JolonB/DualSense-Charging-Dock/assets/images/c.jpg

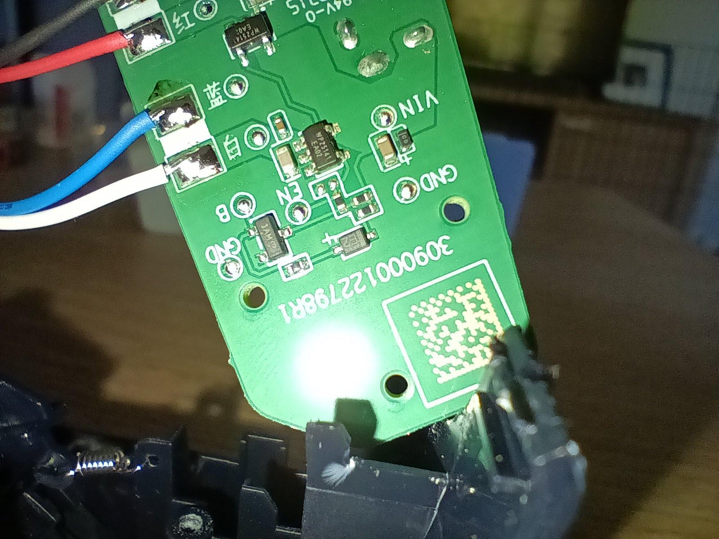
assets/images/c.jpg
