JolonB/DualSense-Charging-Dock/assets/images/g.jpg

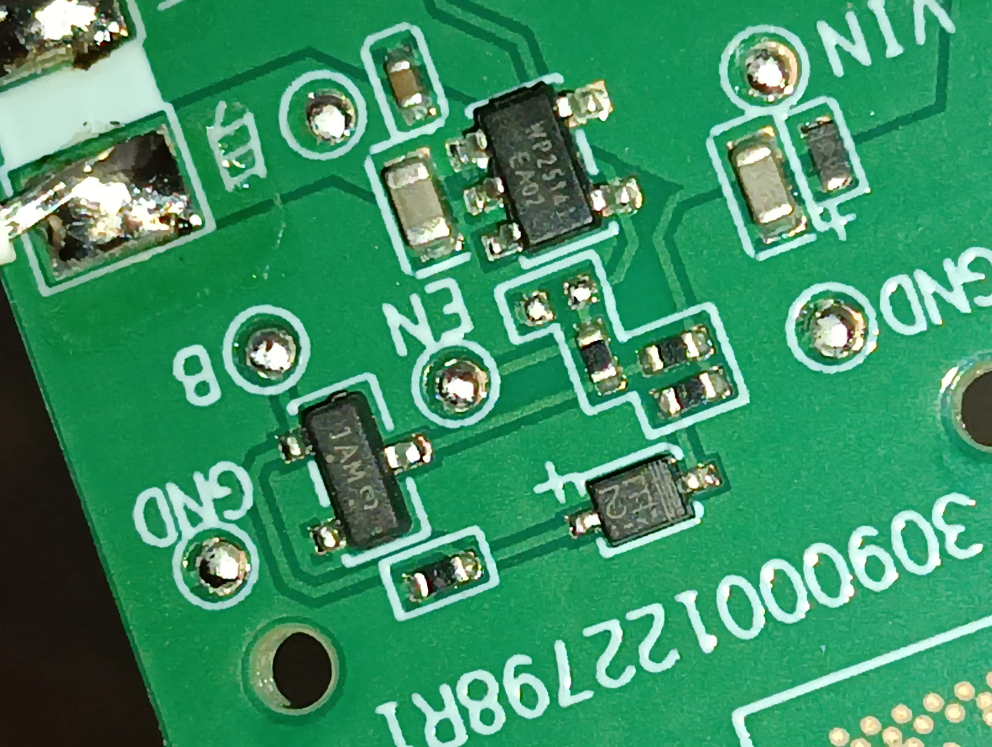
assets/images/g.jpg
